djtulan/nunchuk64/src/joystick.h

//=============================================================================
// *** Nunchuk64 ***
// Copyright (c) Robert Grasböck, All rights reserved.
//
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
// You should have received a copy of the GNU General Public License
// along with this program.  If not, see <http://www.gnu.org/licenses/>.
//=============================================================================
/// @file   joystick.h
/// @author Robert Grasböck (robert.grasboeck@gmail.com)
/// @date   December, 2017
/// @brief  digital joystick part
//=============================================================================
#ifndef _JOYSTICK_H_
#define _JOYSTICK_H_

#include <inttypes.h>

enum Joystick_State {
  // joystick data
  UP        = (1 << 0), ///< up
  DOWN      = (1 << 1), ///< down
  LEFT      = (1 << 2), ///< left
  RIGHT     = (1 << 3), ///< right
  BUTTON    = (1 << 4), ///< fire button
  // special function
  SPACE     = (1 << 5), ///< fire button on port A
  AUTOFIRE  = (1 << 6), ///< auto fire button
  BUTTON2   = (1 << 7), ///< fire button2
  AUTOFIRE2 = (1 << 8), ///< auto fire button2
  BUTTON3   = (1 << 9), ///< fire button3
  AUTOFIRE3 = (1 << 10) ///< auto fire button3
};

/// \brief Joystick, holds the state of one joystick
typedef uint16_t Joystick;

/**
* @brief Init Joystick Ports
*
* All joystick output bits are set to zero
* All joystick ddr bits are set to zero (Tri-state)
* Should be default anyway
*/
extern void joystick_init(void);

/**
* @brief Update Joystick state
*
* @param [in] port_a byte representing the state of Port A
* @param [in] port_b byte representing the state of Port A
*
* The bit (see Joystick_State) are set inside the respective parameter
*/
extern void joystick_update(Joystick port_a, uint8_t ext_a,
                            Joystick port_b, uint8_t ext_b);

/**
* @brief poll joystick routines (for autofire)
* @note This function is called by timer interrupt routine
*/
extern void joystick_poll(void);

#endif
